backwardn/siginttablet/3d models/1 top bezel case/top bezel case.jpg00.png

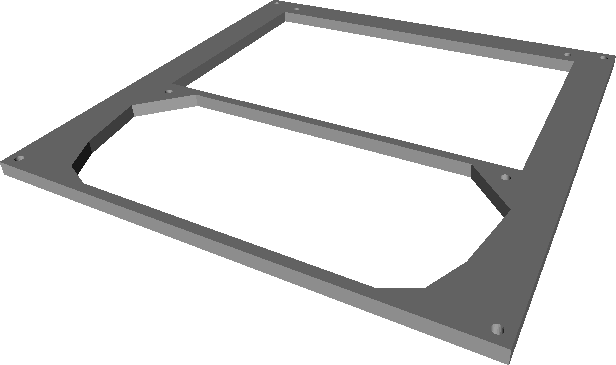
3d models/1 top bezel case/top bezel case.jpg00.png
