backwardn/siginttablet/3d models/2 lcd backplane/lcd backplane.jpg00.png

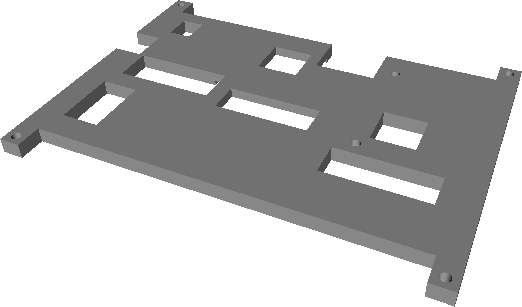
3d models/2 lcd backplane/lcd backplane.jpg00.png
