backwardn/siginttablet/3d models/3 exterior back/exterior back crazyradio.jpg00.png

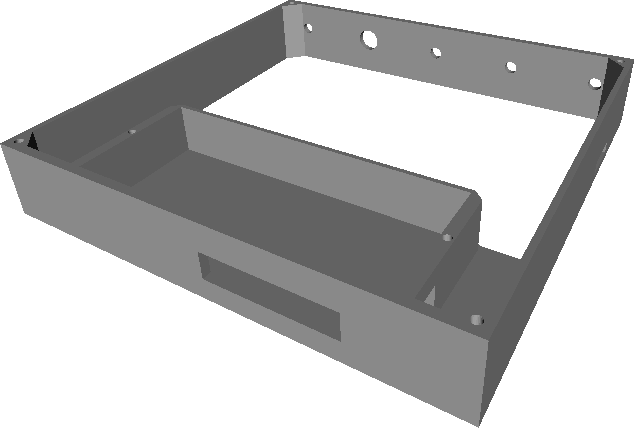
3d models/3 exterior back/exterior back crazyradio.jpg00.png
