backwardn/siginttablet/3d models/4 battery bar/battery bar.jpg00.png

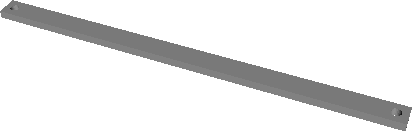
3d models/4 battery bar/battery bar.jpg00.png
