backwardn/siginttablet/3d models/5 back plate/back plate.jpg00.png

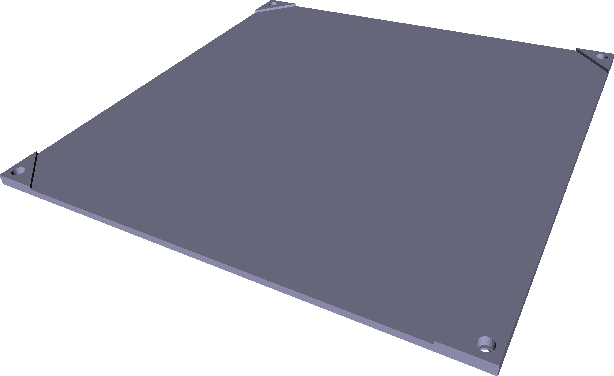
3d models/5 back plate/back plate.jpg00.png
