backwardn/siginttablet/3d models/6 antenna case/bottom.jpg00.png

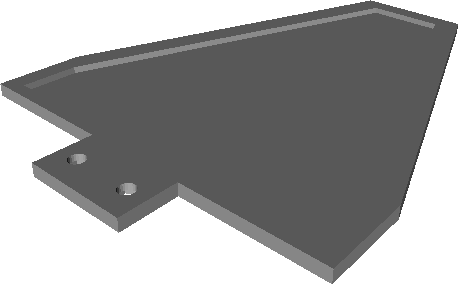
3d models/6 antenna case/bottom.jpg00.png
