backwardn/siginttablet/3d models/6 antenna case/log period.jpg

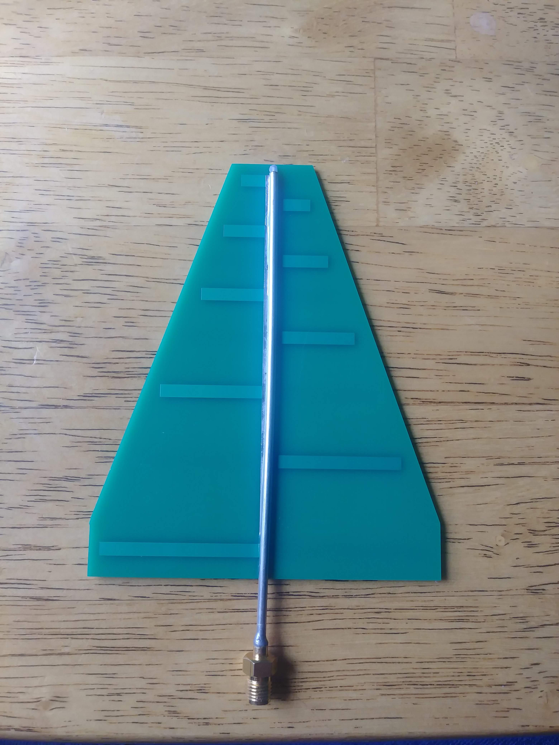
3d models/6 antenna case/log period.jpg
