backwardn/siginttablet/3d models/6 antenna case/top.jpg00.png

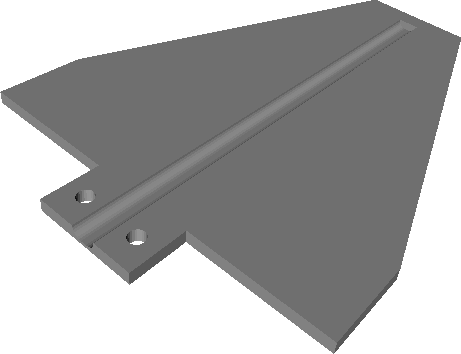
3d models/6 antenna case/top.jpg00.png
