backwardn/siginttablet/3d models/7 gps holder/gps holder.jpg00.png

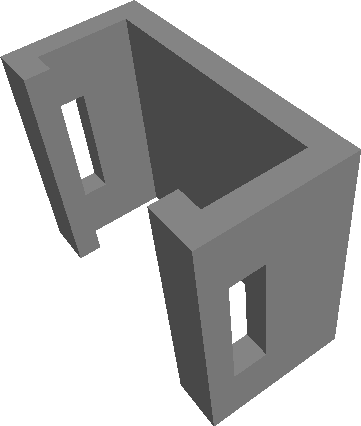
3d models/7 gps holder/gps holder.jpg00.png
