backwardn/siginttablet/CircleCityCon 2019/assets/4cb55e70e5cec82ab70782f7a86980137fd862884ff9093f4bc6f484e5d9a9f0.jpg

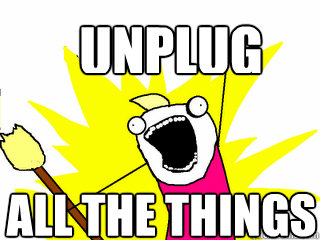
CircleCityCon 2019/assets/4cb55e70e5cec82ab70782f7a86980137fd862884ff9093f4bc6f484e5d9a9f0.jpg
