backwardn/siginttablet/CircleCityCon 2019/assets/4qam.png

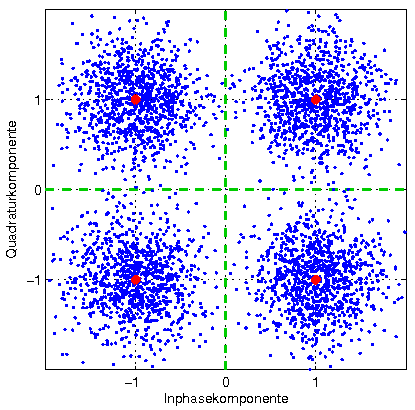
CircleCityCon 2019/assets/4qam.png
