backwardn/siginttablet/CircleCityCon 2019/assets/12n8c2.jpg

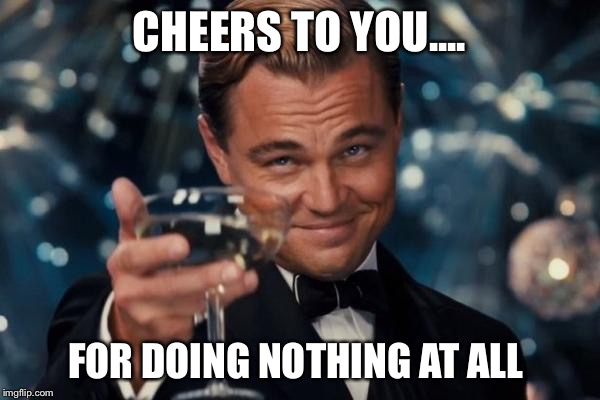
CircleCityCon 2019/assets/12n8c2.jpg
