backwardn/siginttablet/CircleCityCon 2019/assets/analog.JPG

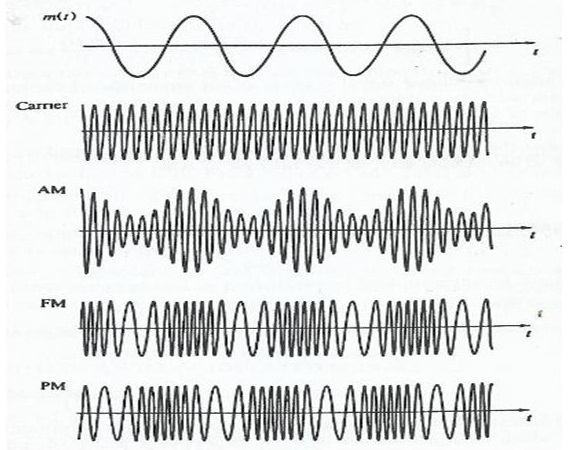
CircleCityCon 2019/assets/analog.JPG
