backwardn/siginttablet/CircleCityCon 2019/assets/frame.png

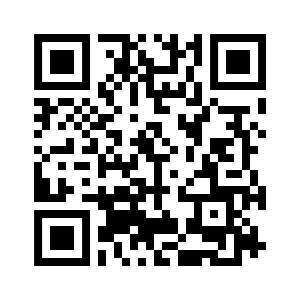
CircleCityCon 2019/assets/frame.png
