backwardn/siginttablet/CircleCityCon 2019/assets/gnuradio with gedit.png

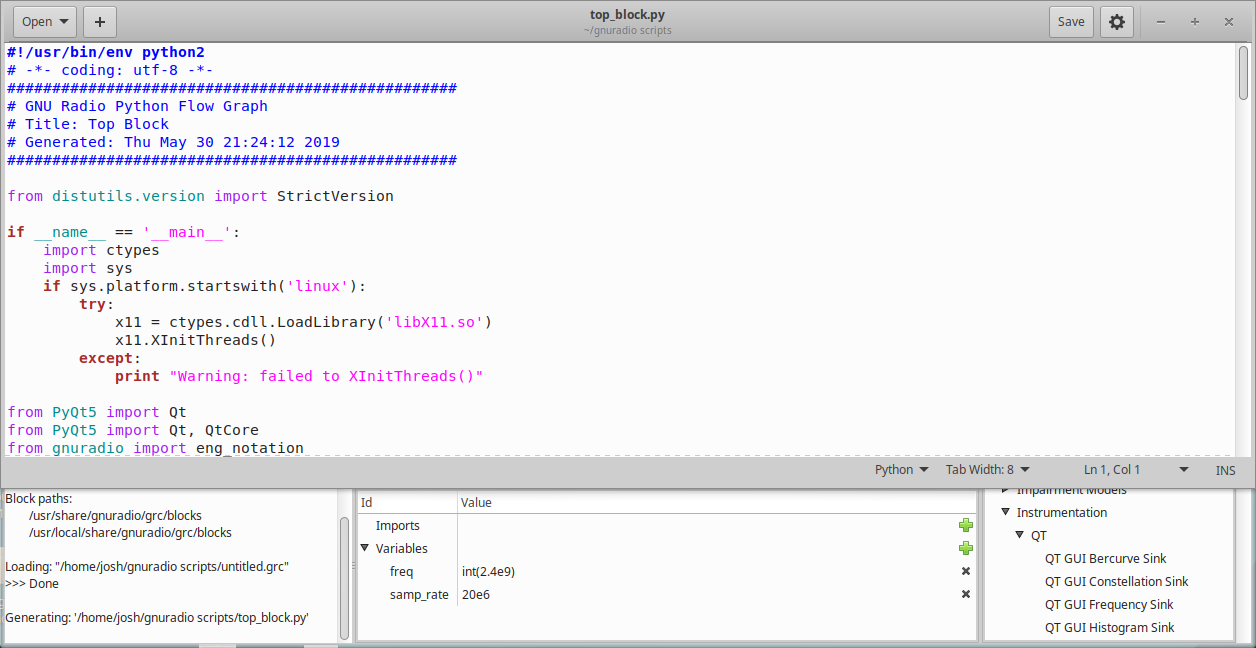
CircleCityCon 2019/assets/gnuradio with gedit.png
