backwardn/siginttablet/CircleCityCon 2019/assets/modulation.jpg

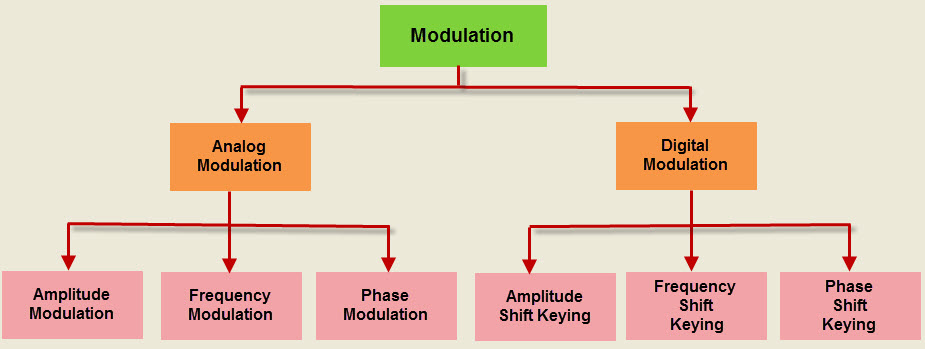
CircleCityCon 2019/assets/modulation.jpg
