backwardn/siginttablet/CircleCityCon 2019/assets/shift keying.png

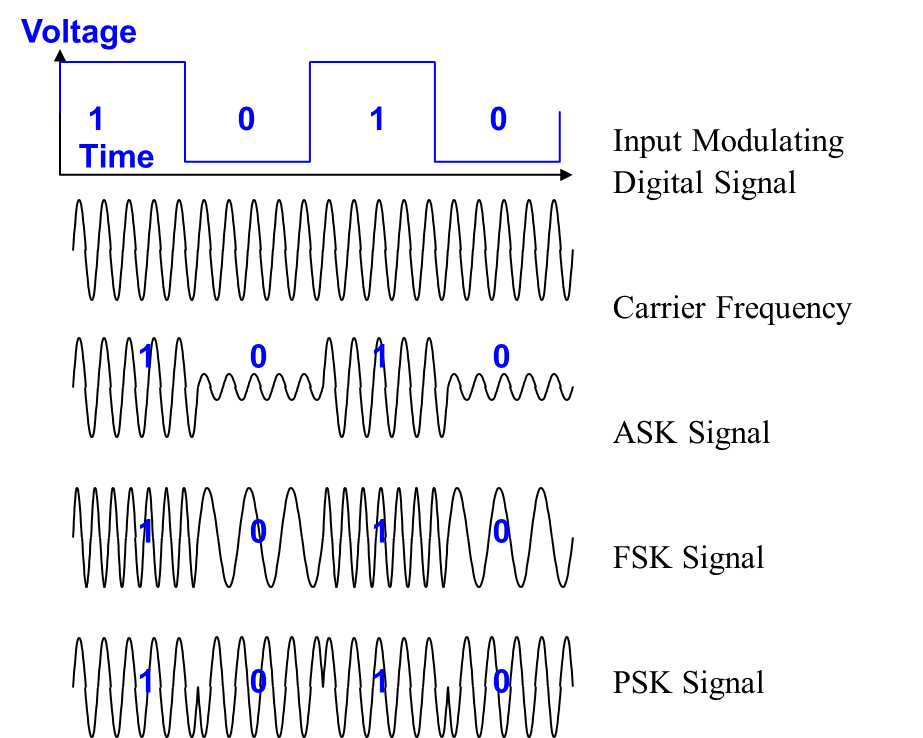
CircleCityCon 2019/assets/shift keying.png
