backwardn/siginttablet/CircleCityCon 2019/assets/Untitled.png

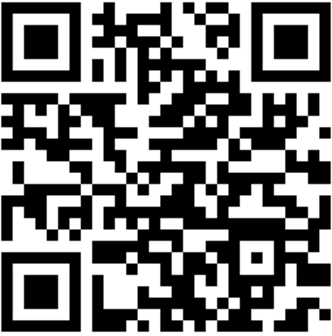
CircleCityCon 2019/assets/Untitled.png
