backwardn/siginttablet/CircleCityCon 2019/assets/WiFi-Eye.png

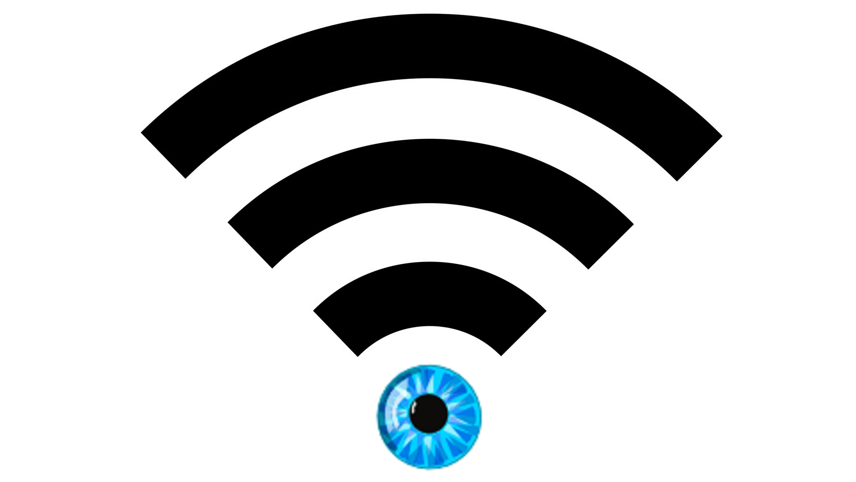
CircleCityCon 2019/assets/WiFi-Eye.png
