backwardn/siginttablet/CircleCityCon 2019/assets/yagi.jpg

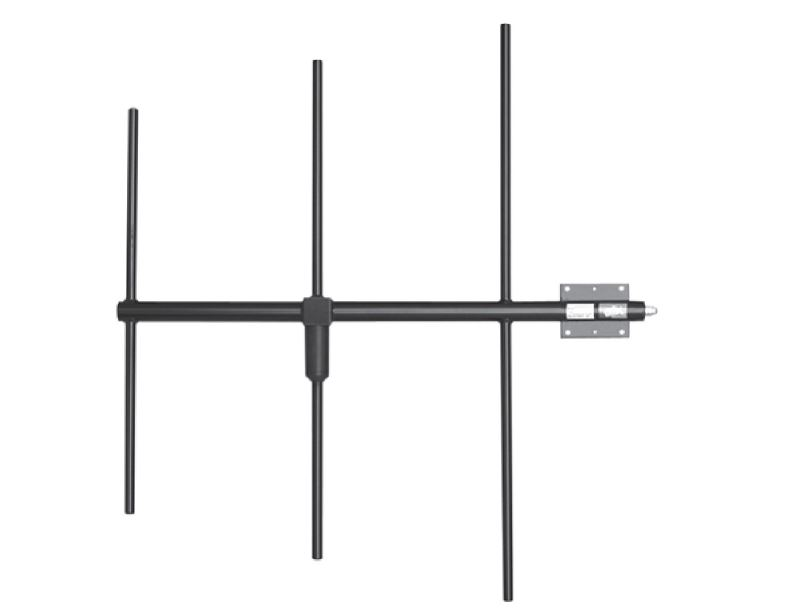
CircleCityCon 2019/assets/yagi.jpg
